FEDEVEL/custom-keyboard/Hardware/Manufacturing/For All Boxes/plate_for_industrial_printing_2mm.stl

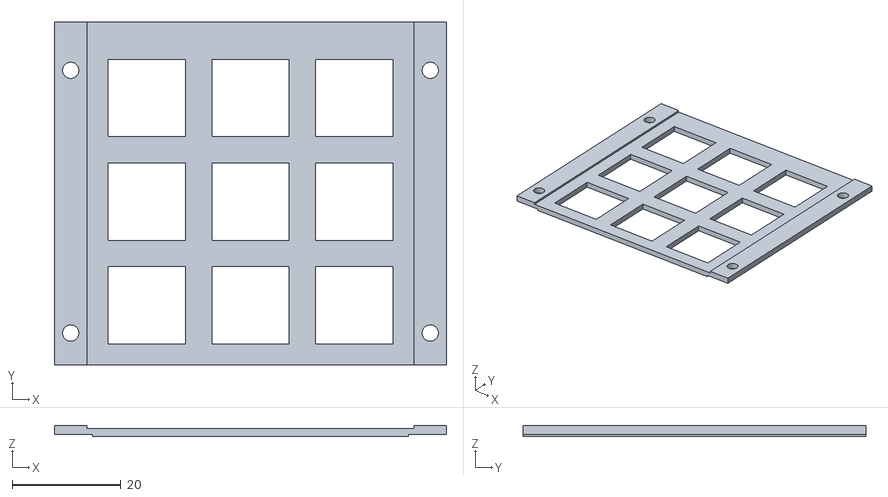
[picture p17: CAD file, 2024-11-01]
Hardware/Manufacturing/For All Boxes/plate_for_industrial_printing_2mm.stl
72.0 x 63.0 x 2.00
